dejanpan/Home-Monitoring-Raspberry-Pi-Node/pics/webcam.jpg

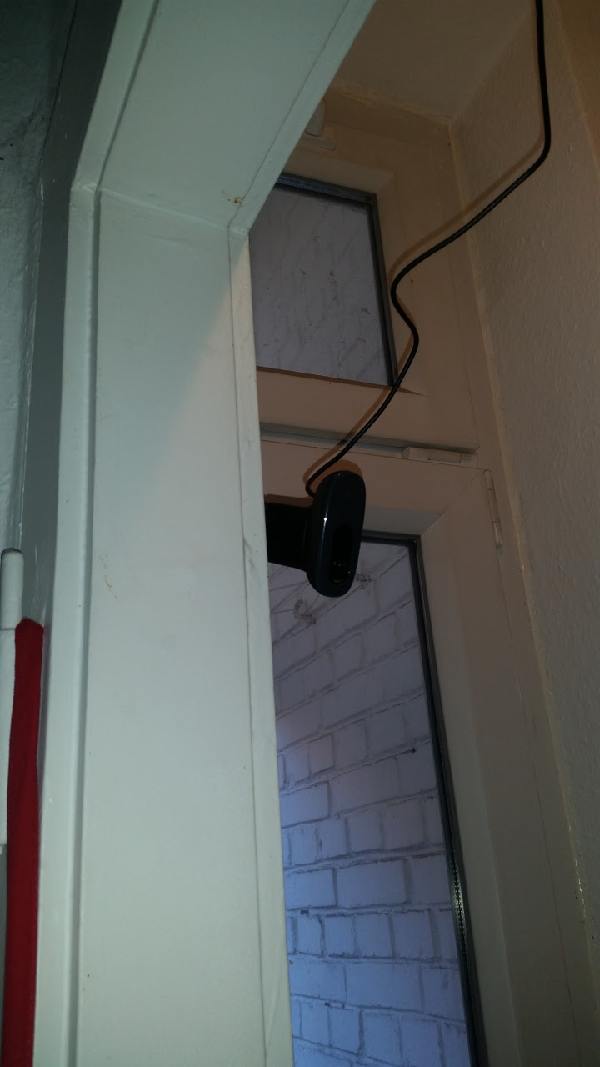
pics/webcam.jpg
