dejanpan/Home-Monitoring-Raspberry-Pi-Node/static/fridge_small.png

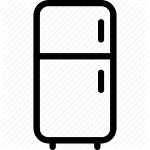
static/fridge_small.png
