dejanpan/Home-Monitoring-Raspberry-Pi-Node/static/lights_small.png

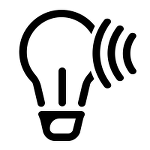
static/lights_small.png
