dejanpan/Home-Monitoring-Raspberry-Pi-Node/static/security_small.png

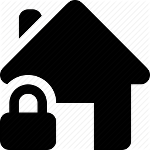
static/security_small.png
